jojelupipa/smart-plug/src/dummy_examples/ESP32-SCT013/Frec 6 seg.png

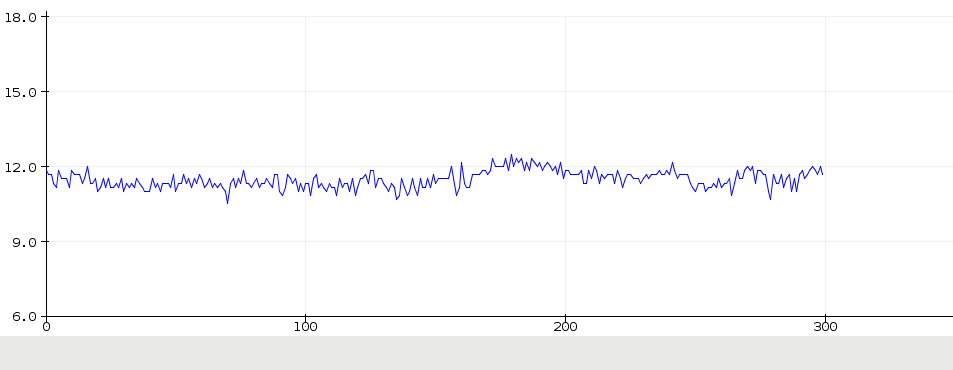
src/dummy_examples/ESP32-SCT013/Frec 6 seg.png
