jojelupipa/smart-plug/src/dummy_examples/ESP32-SCT013/Muestreo a distintas frecuencias.png

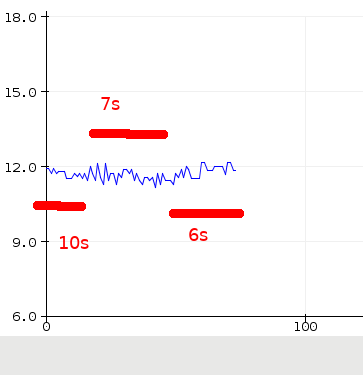
src/dummy_examples/ESP32-SCT013/Muestreo a distintas frecuencias.png
